MartinReinhard10/In-Situ_Soil_Optode_Supplementary_Material/3D printing (.stl)/Camera_holder.stl

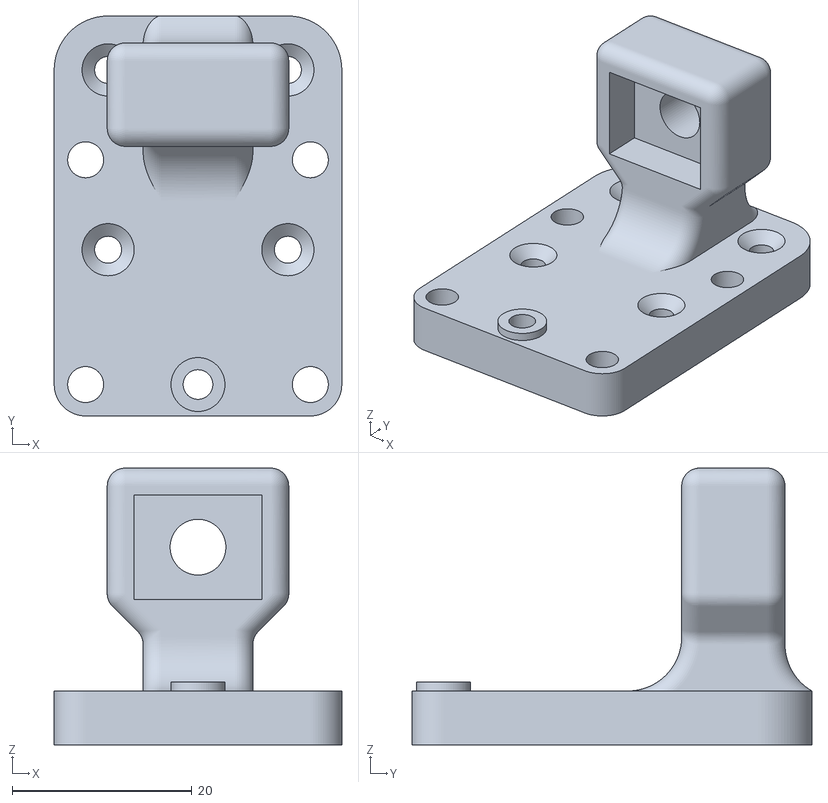
[picture p15: CAD file, 2024-10-11]
3D printing (.stl)/Camera_holder.stl
32.0 x 44.5 x 30.8
