MartinReinhard10/In-Situ_Soil_Optode_Supplementary_Material/3D printing (.stl)/Lens_filter_mount.stl

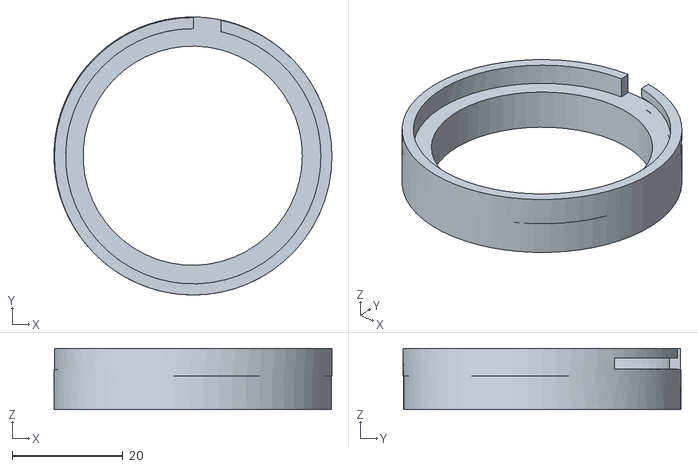
[picture p16: CAD file, 2024-10-11]
3D printing (.stl)/Lens_filter_mount.stl
50.1 x 50.1 x 11.0
