MartinReinhard10/In-Situ_Soil_Optode_Supplementary_Material/3D printing (.stl)/Rail_mount_top_glider.stl

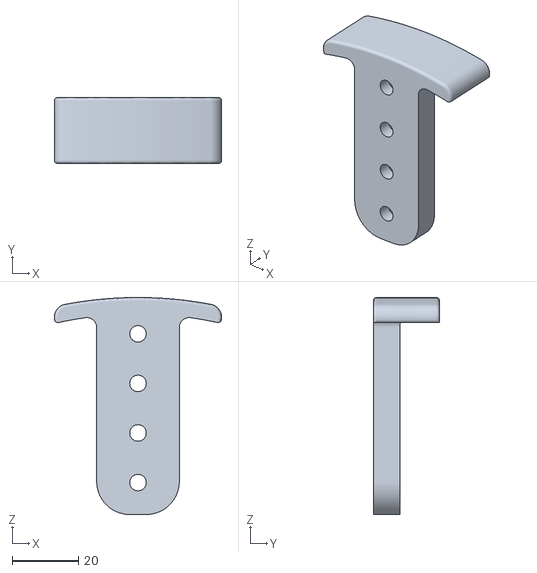
[picture p17: CAD file, 2024-10-11]
3D printing (.stl)/Rail_mount_top_glider.stl
50.6 x 20.0 x 65.7
