MartinReinhard10/In-Situ_Soil_Optode_Supplementary_Material/3D printing (.stl)/Rotation_gear.stl

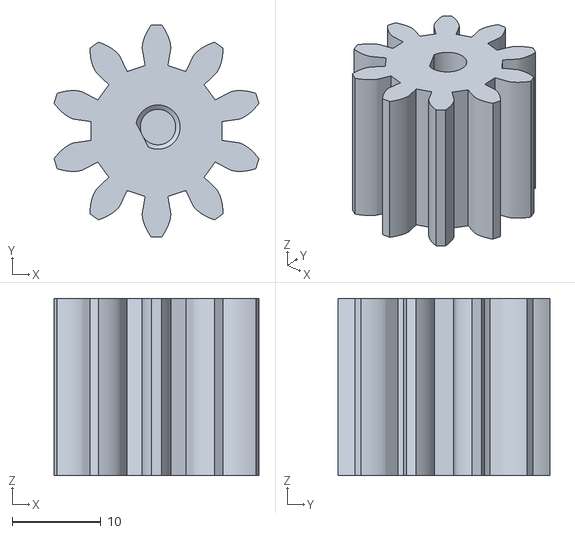
[picture p18: CAD file, 2024-10-11]
3D printing (.stl)/Rotation_gear.stl
23.2 x 24.0 x 20.0
