MartinReinhard10/In-Situ_Soil_Optode_Supplementary_Material/3D printing (.stl)/Gear_ring_V2.stl

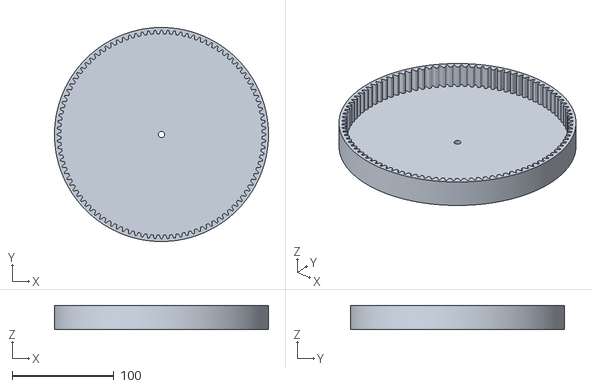
[picture p19: CAD file, 2024-10-11]
3D printing (.stl)/Gear_ring_V2.stl
210.0 x 210.0 x 24.0
