MartinReinhard10/In-Situ_Soil_Optode_Supplementary_Material/3D printing (.stl)/Rail_mount_top.stl

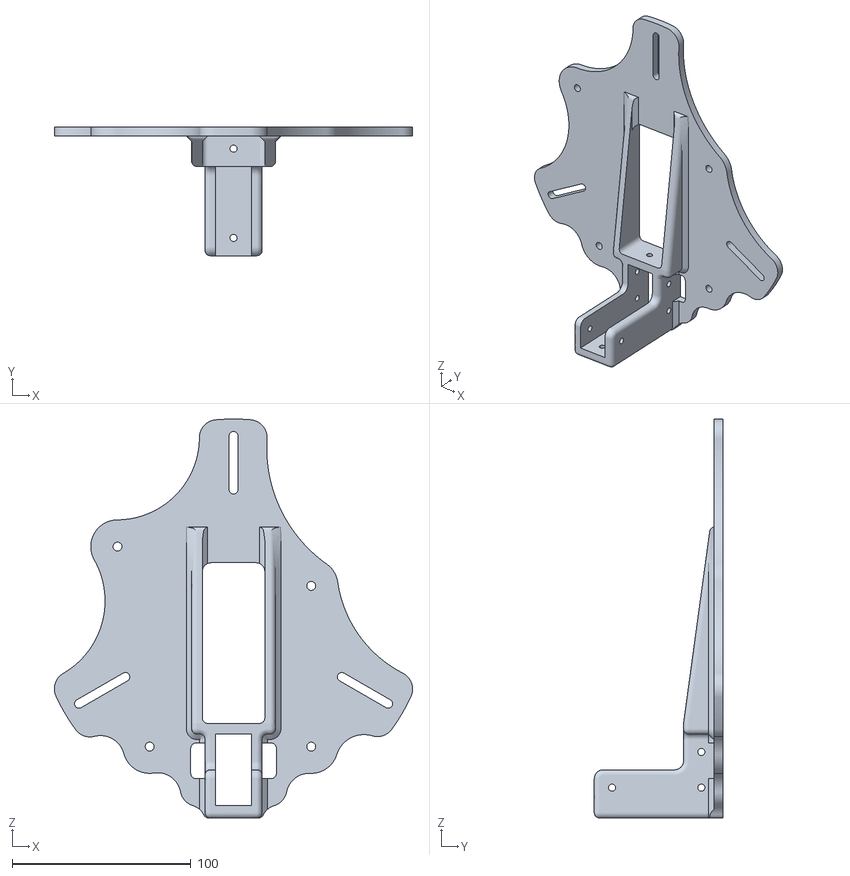
[picture p20: CAD file, 2024-10-11]
3D printing (.stl)/Rail_mount_top.stl
200.7 x 72.0 x 223.5
